simi1505/5-Band-50W-PA-OE3SDE/50W PA/Eagle Files/5-Band 50W PA_50W PA_Pics/5-Band 50W PA_50W PA_Drills.png

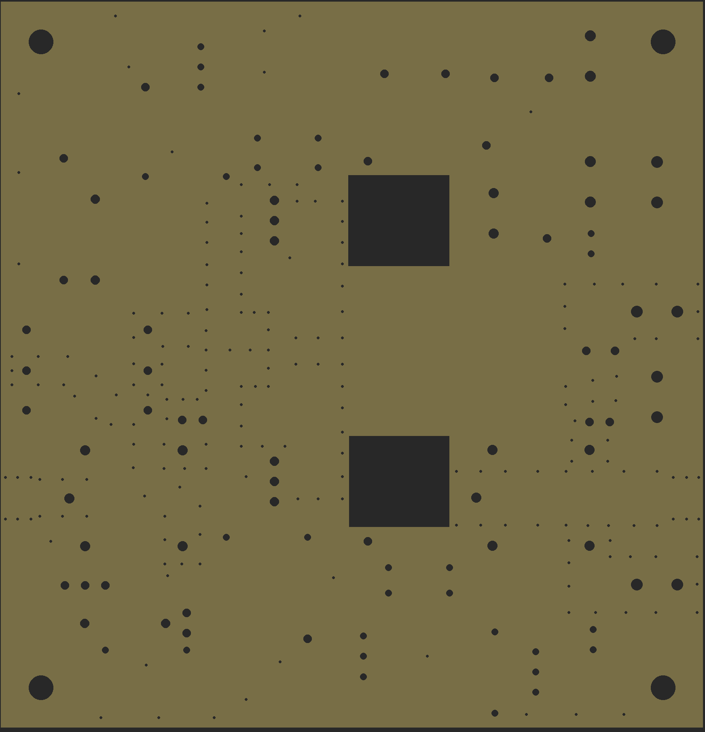
50W PA/Eagle Files/5-Band 50W PA_50W PA_Pics/5-Band 50W PA_50W PA_Drills.png
