simi1505/5-Band-50W-PA-OE3SDE/LC Lowpass Filters/Eagle Files/5-Band 50W PA_LC Lowpass Filters_Pics/5-Band 50W PA_LC Lowpass Filters_BOT.png

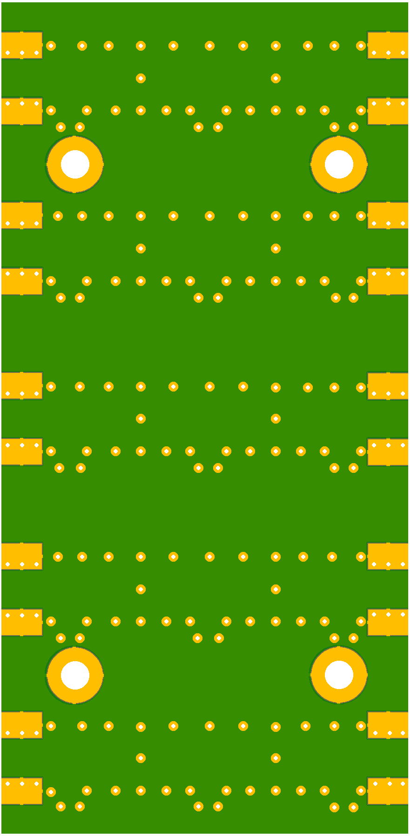
LC Lowpass Filters/Eagle Files/5-Band 50W PA_LC Lowpass Filters_Pics/5-Band 50W PA_LC Lowpass Filters_BOT.png
