simi1505/5-Band-50W-PA-OE3SDE/LC Lowpass Filters/Measurements/30m_2.png

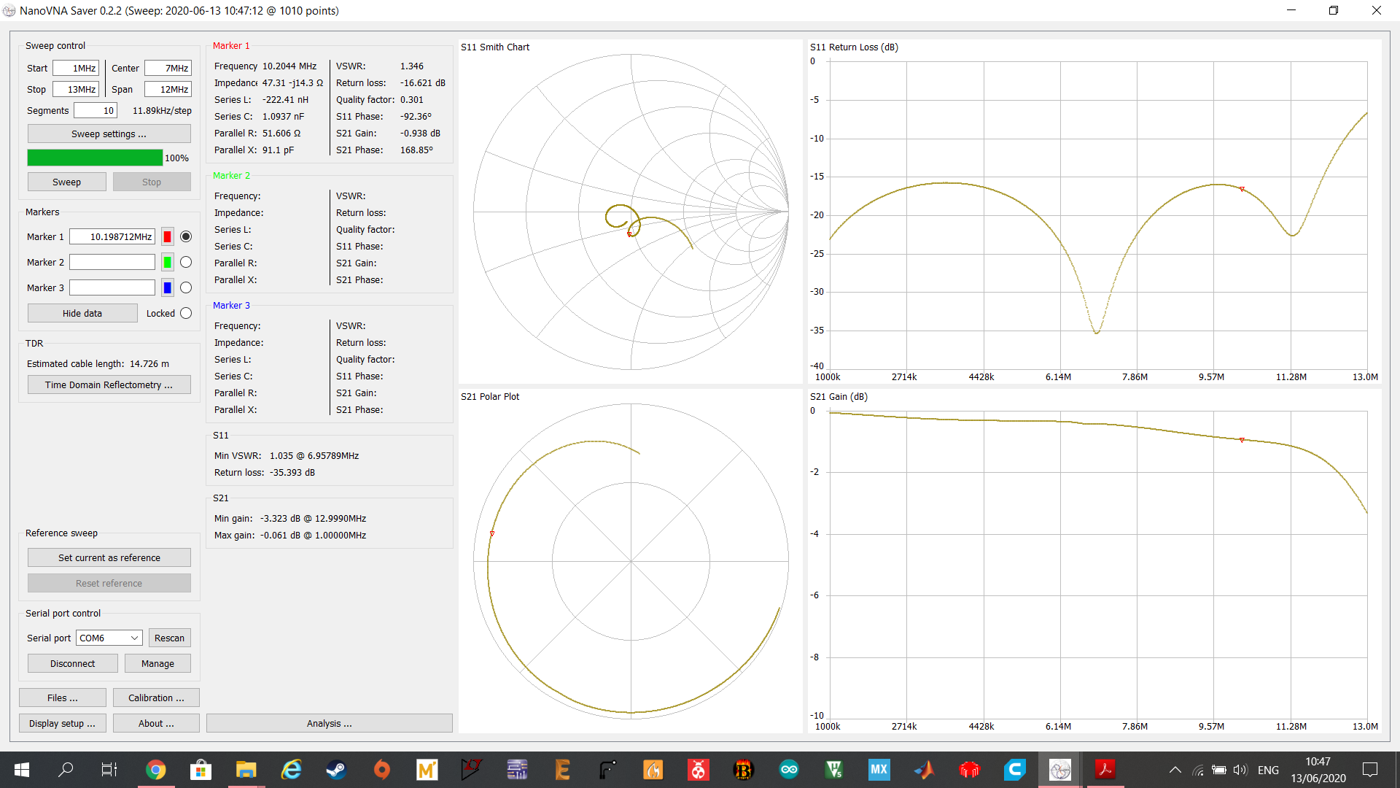
LC Lowpass Filters/Measurements/30m_2.png
