simi1505/5-Band-50W-PA-OE3SDE/50W PA/Simulations/50W PA with OCP.asc

C1: cap; 100n
C2: cap; 100n
C3: cap; 100n
C4: cap; 100nF
C5: cap; 2200µF
C6: cap; 100nF
C7: cap; 100n
C8: cap; 500p
C9: cap; 1n
C10: cap; 100n
C11: cap; 10µ
C12: cap; 180p
C13: cap; 330p
C14: cap; 180p
D1: diode; 1N4148
D2: diode; 1N4148
D3: diode; 1N4148
D4: diode; 1N4148
D5: diode; 1N4148
D6: diode; 1N4148
D9: diode; 1N4148
D10: diode; 1N4148
D11: diode; 1N4148
D12: diode; 1N4148
D13: diode; 1N4148
D14: diode; 1N4148
D15: diode; 1N4148
L1: ind2; 1.75µ
L2: ind2; 1.75µ
L3: ind2; 63µ
L4: ind2; 8.75µ
L5: ind2; 22.4µ
L6: ind; 580n
L7: ind; 580n
M1: nmos; IRF510
M2: nmos; IRF510
Q1: pnp; BC557B
Q2: pnp; BC557B
Q3: npn; TIP31C
Q4: pnp; TIP32C
Q5: pnp; BC557C
R1: res; 300
R2: res; 300
R3: res; 50
R4: res; 18
R5: res; 3.9k
R6: res; 7.5k
R7: res; 2.5k
R8: res; 150
R9: res; 100
R10: res; 10k
R11: res; 10
R12: res; 10
R13: res; 0.1
R14: res; 3.9k
R15: res; 7.5k
R16: res; 100
R17: res; 2.5k
R18: res; 150
R19: res; 10k
R20: res; 2k
R21: res; 0.15
R22: res; 100
R24: res; 470
R25: res; 250
R26: res; 340
V1: voltage; SINE(0 20 14200000); AC 0
V3: voltage; 12
V4: voltage; 10
V5: voltage; SINE(0 5 30000000); AC 1
Named nets: 0
K2 L1 L2 L3 1
K2 L4 L5 1
.tran 0.001
50W PA with Bias Circuit
RF-Sensing RX/TX Switch
Overcurrent Protection Circuit
0.25W (5Vp) to 25W (50Vp)
