simi1505/5-Band-50W-PA-OE3SDE/50W PA/Simulations/50W PA.asc

C1: cap; 100n
C2: cap; 100n
C3: cap; 100n
C4: cap; 100nF
C5: cap; 2200µF
C6: cap; 100nF
C7: cap; 100n
C8: cap; 500p
C9: cap; 1n
C10: cap; 100n
C11: cap; 10µ
C12: cap; 180p
C13: cap; 330p
C14: cap; 180p
D1: diode; 1N4148
D2: diode; 1N4148
D3: diode; 1N4148
D4: diode; 1N4148
D9: diode; 1N4148
D10: diode; 1N4148
D14: diode; 1N4148
D15: diode; 1N4148
L1: ind2; 1.75µ
L2: ind2; 1.75µ
L3: ind2; 63µ
L4: ind2; 8.75µ
L5: ind2; 22.4µ
L6: ind; 580n
L7: ind; 580n
M1: nmos; IRF510
M2: nmos; IRF510
Q1: pnp; BC557B
Q2: pnp; BC557B
Q3: npn; TIP31C
R1: res; 300
R2: res; 300
R3: res; 50
R4: res; 18
R5: res; 1k
R6: res; 500
R7: res; 500
R8: res; 330
R9: res; 100
R10: res; 10k
R11: res; 10
R12: res; 10
R13: res; 0.1
R14: res; 1k
R15: res; 500
R16: res; 100
R17: res; 500
R18: res; 330
R24: res; 470
R25: res; 250
R26: res; 340
V1: voltage; SINE(0 20 14200000); AC 0
V3: voltage; 13.8
V4: voltage; 10
V5: voltage; SINE(0 5 30000000); AC 1
Named nets: 0
K2 L1 L2 L3 1
K2 L4 L5 1
.tran 0.001
50W PA with Bias Circuit
RF-Sensing RX/TX Switch
0.25W (5Vp) to 25W (50Vp)
