simi1505/5-Band-50W-PA-OE3SDE/LC Lowpass Filters/Simulations/LC Lowpass Filters.asc

180: cap; 164p
C1: cap; 820p
C2: cap; 1500p
C3: cap; 820p
C4: cap; 560p
C5: cap; 1000p
C6: cap; 560p
C7: cap; 330p
C8: cap; 560p
C9: cap; 330p
C10: cap; 180p
C11: cap; 330p
C12: cap; 180p
C13: cap; 82p
C15: cap; 82p
L1: ind; 2.5µ
L2: ind; 2.5µ
L3: ind; 1.2µ
L4: ind; 1.2µ
L5: ind; 1µ
L6: ind; 1µ
L7: ind; 580n
L8: ind; 580n
L9: ind; 400n
L10: ind; 400n
R2: res; 50
R4: res; 50
R6: res; 50
R8: res; 50
R10: res; 50
V1: voltage; SINE(0 1 1); AC 1
V2: voltage; SINE(0 1 1); AC 1
V3: voltage; SINE(0 1 1); AC 1
V4: voltage; SINE(0 1 1); AC 1
V5: voltage; SINE(0 1 1); AC 1
Named nets: 0
.ac dec 1000 1000000 100000000
80m (fc = 4.9MHz)
40m (fc = 8.8MHz)
30m (fc = 12.5MHz)
20m & 17m (fc = 21.6MHz)
15m & 10m (fc = 35.85MHz)
5-Band LC Lowpass Filters
